computergeek1507/sb_pixel_16/firmware/SBPixel16/page_index.h

#pragma once

// GET /api/status  — live runtime stats
void get_status(AsyncWebServerRequest *request) {
    char buf[640];
    const char *proto = cfg.protocol == PROTO_DDP  ? "ddp"
                      : cfg.protocol == PROTO_FSEQ ? "fseq"
                                                   : "e131";
    snprintf(buf, sizeof(buf),
        "{\"fps\":%lu,\"e131Packets\":%lu,\"ddpPackets\":%lu"
        ",\"protocol\":\"%s\""
        ",\"vin1_mv\":%lu,\"vin2_mv\":%lu"
        ",\"testMode\":%u"
        ",\"sdMounted\":%s,\"sdSizeMB\":%lu,\"fseqCount\":%u"
        ",\"fseqName\":\"%s\",\"fseqFrame\":%lu,\"fseqFrames\":%lu"
        ",\"version\":\"%s\",\"build\":%u,\"buildDate\":\"%s\""
        ",\"parlioOk\":%s,\"menuActive\":%s,\"b1HeldMs\":%lu"
        ",\"otaMode\":%u,\"otaFlashMs\":%lu,\"freePsram\":%lu,\"psramSize\":%lu"
        ",\"sdError\":\"%s\"}",
        (unsigned long)g_fps,
        (unsigned long)g_e131Packets,
        (unsigned long)g_ddpPackets,
        proto,
        (unsigned long)g_vin1_mv,
        (unsigned long)g_vin2_mv,
        g_testMode,
        g_sdMounted ? "true" : "false",
        (unsigned long)g_sdSizeMB,
        g_fseqCount,
        g_fseqName,
        (unsigned long)g_fseqFrame,
        (unsigned long)g_fseqFrames,
        FW_VERSION, (unsigned)FW_BUILD, FW_BUILD_DATE,
        g_parlioOk ? "true" : "false",
        g_menuActive ? "true" : "false",
        (unsigned long)g_b1HeldMs,
        (unsigned)g_otaMode,
        (unsigned long)g_otaFlashMs,
        (unsigned long)ESP.getFreePsram(),
        (unsigned long)ESP.getPsramSize(),
        g_sdError);
    request->send(200, "application/json", buf);
}
